Rikeroo/habit-reminder/firmware/habit-reminder-c6/main/lvgl_ui.c

#include "lvgl.h"

void lvgl_ui_demo(lv_disp_t *disp)
{
    lv_obj_t *scr = lv_disp_get_scr_act(disp);
    lv_obj_t *label = lv_label_create(scr);
    lv_label_set_long_mode(label, LV_LABEL_LONG_SCROLL_CIRCULAR);
    lv_label_set_text(label, "Look at me goooooo");
    lv_obj_set_width(label, disp->driver->hor_res);
    lv_obj_align(label, LV_ALIGN_TOP_MID, 0, 0);

}
